SolderedElectronics/Ultrasonic-sensor-qwiic-hardware-design/OUTPUTS/V1.1.1/333001.jpg

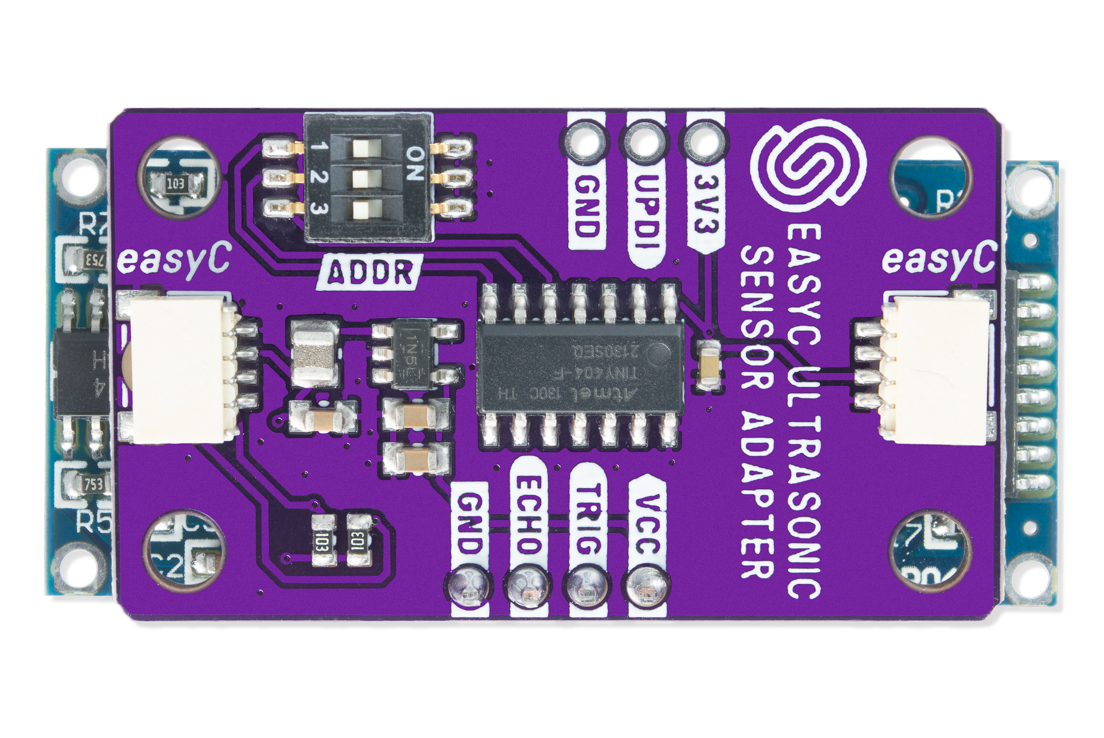
OUTPUTS/V1.1.1/333001.jpg
