SolderedElectronics/Ultrasonic-sensor-qwiic-hardware-design/OUTPUTS/V1.1.1/Ultrasonic sensor with easyC Pinout.jpg

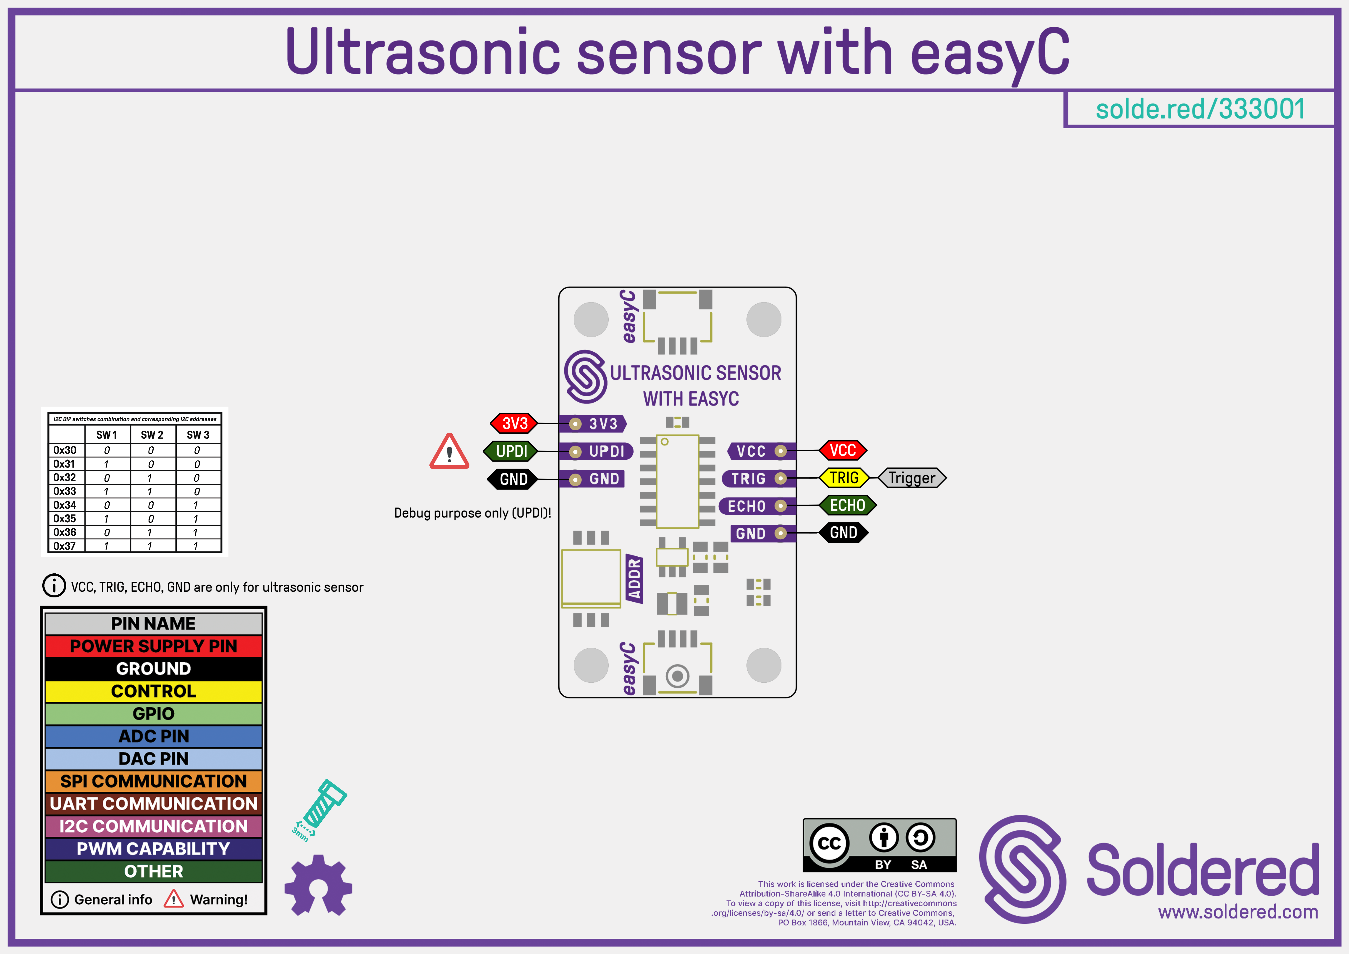
OUTPUTS/V1.1.1/Ultrasonic sensor with easyC Pinout.jpg
